chrisistansell/Cyborg-Trackzeron/3D Print Files/Archives/STL Files - 34mm V3 Snap Fit/Final Top - Bearings 2 bottom 1 top.stl

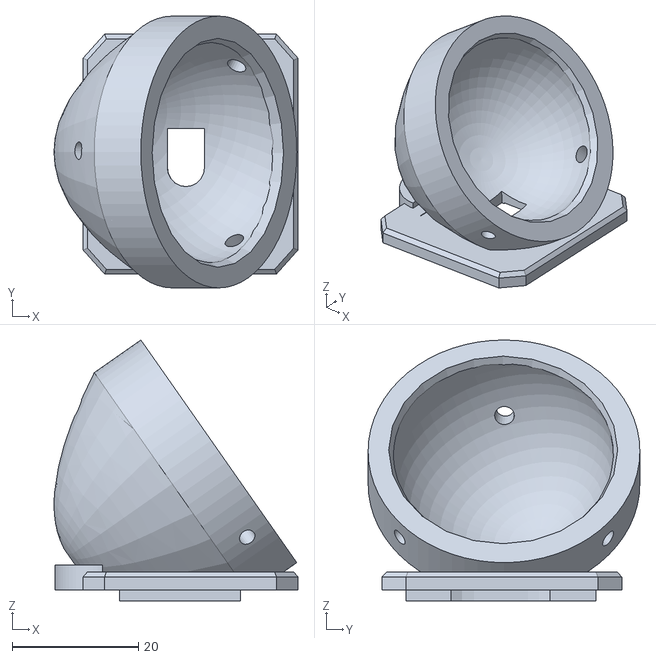
[picture p25: CAD file, 2024-03-11, an earlier design]
3D Print Files/Archives/STL Files - 34mm V3 Snap Fit/Final Top - Bearings 2 bottom 1 top.stl
38.6 x 43.0 x 41.3
