chrisistansell/Cyborg-Trackzeron/3D Print Files/Archives/STL Files - 34mm/40.5-35-34mm no hook.STL

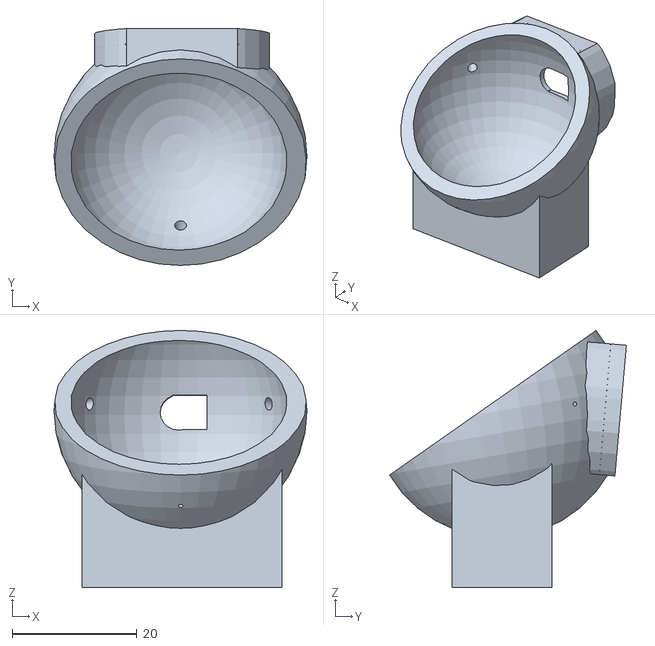
[picture p26: CAD file, 2024-01-19, an earlier design]
3D Print Files/Archives/STL Files - 34mm/40.5-35-34mm no hook.STL
40.5 x 37.9 x 41.1
