chrisistansell/Cyborg-Trackzeron/3D Print Files/Archives/34mm Files - For Angled Position for Terminal Block/Traclzeron Tagged Shroud - for term block cover.3mf

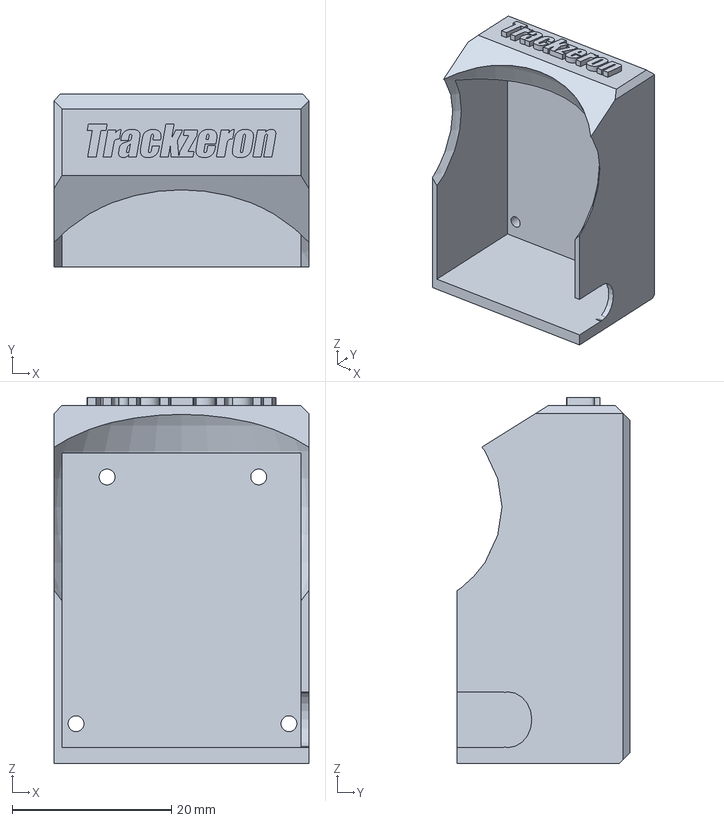
[picture p27: CAD file, 2024-01-28, an earlier design]
3D Print Files/Archives/34mm Files - For Angled Position for Terminal Block/Traclzeron Tagged Shroud - for term block cover.3mf
32.0 x 21.8 x 46.0 mm
